sciguy14/HelioWatcher/GRAPHING AND COLLECTION/heliowatcher_monitor/data/display.jpg

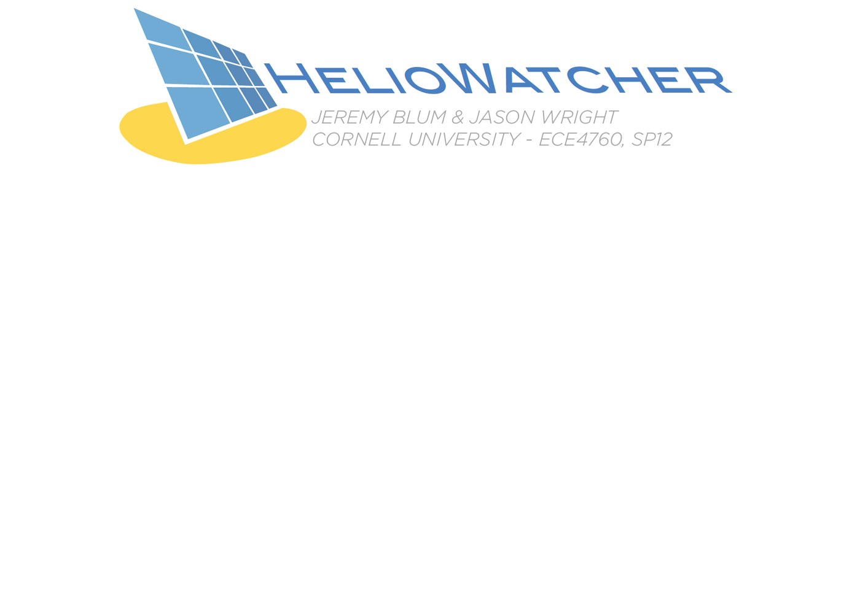
GRAPHING AND COLLECTION/heliowatcher_monitor/data/display.jpg
